cristianoag/trhmsx/images/2023-11-26_15-43.png

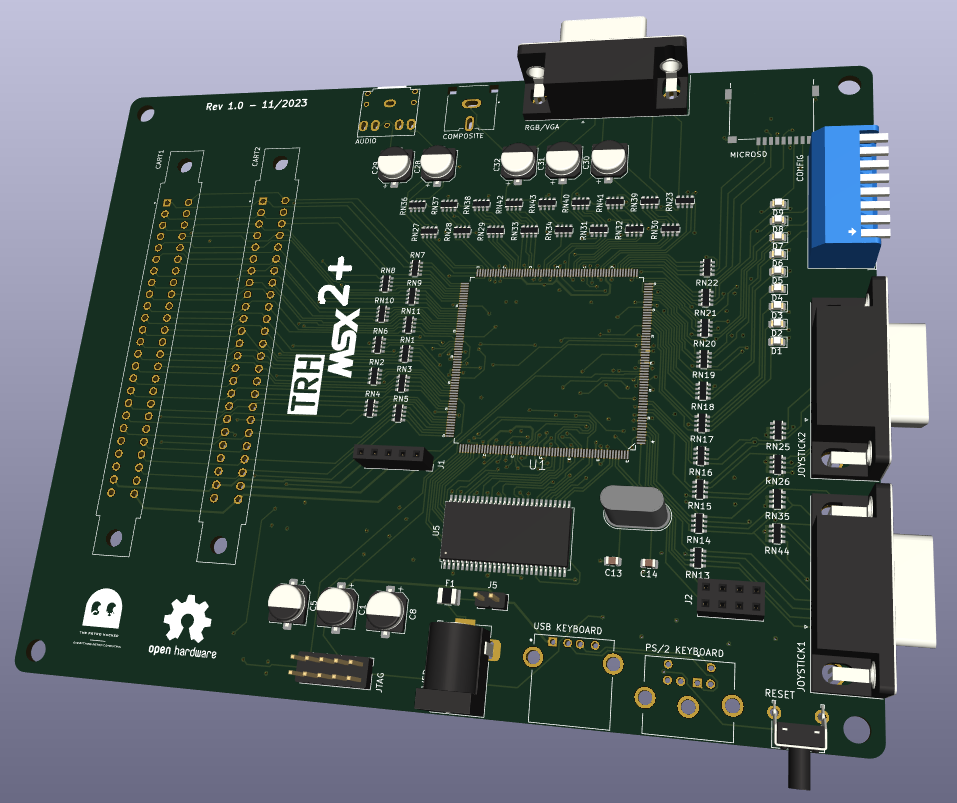
images/2023-11-26_15-43.png
