cristianoag/trhmsx/images/2024-02-25_20-27.png

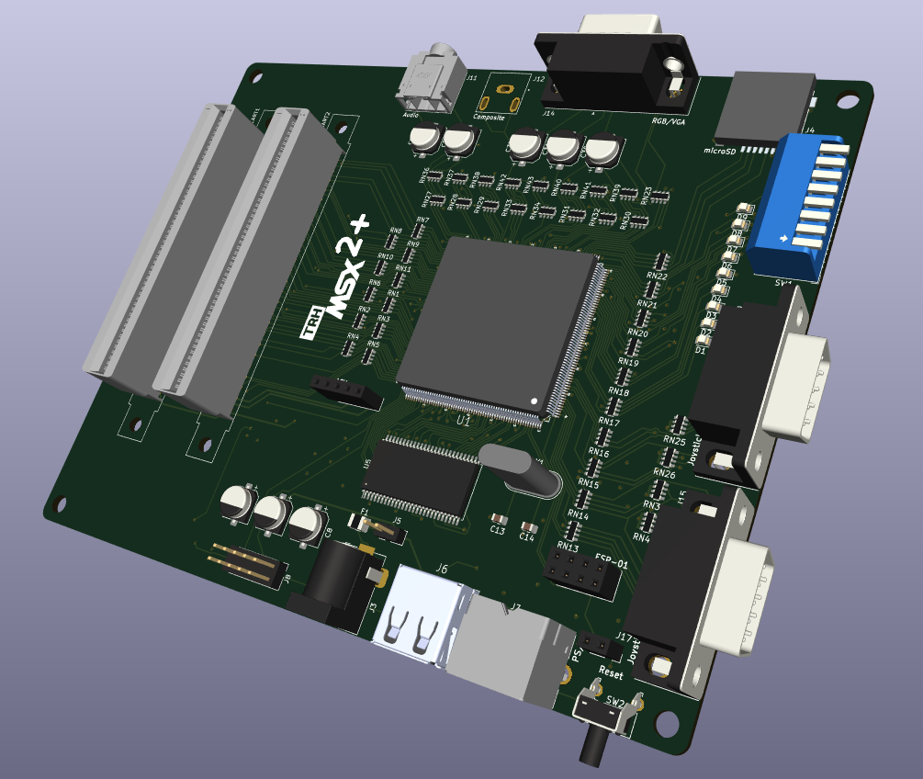
images/2024-02-25_20-27.png
