cristianoag/trhmsx/images/2024-02-25_21-25.png

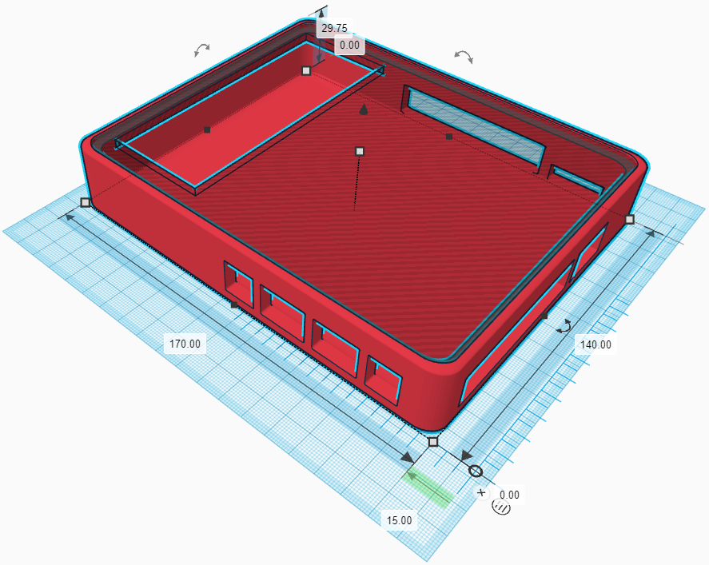
images/2024-02-25_21-25.png
