cristianoag/trhmsx/images/2024-04-27_21-23.png

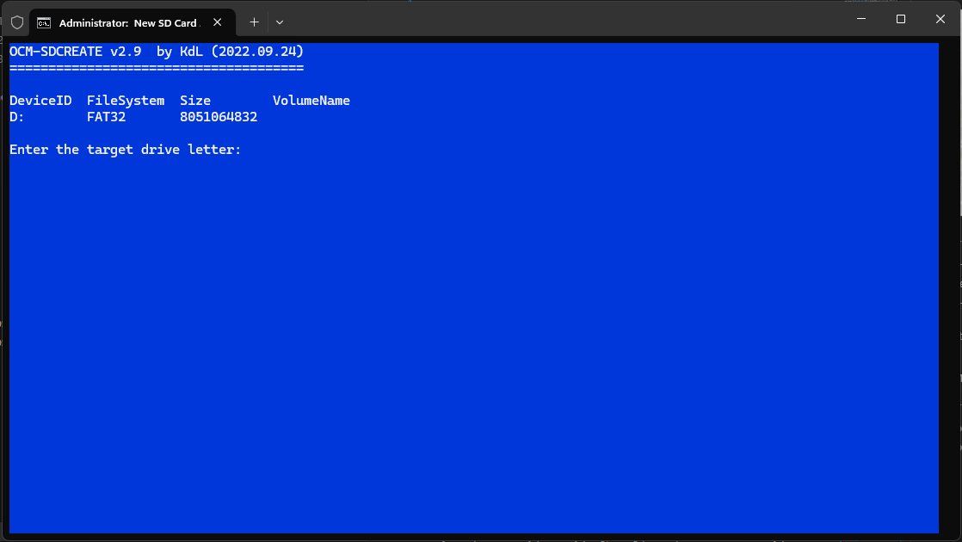
images/2024-04-27_21-23.png
