cristianoag/trhmsx/images/2024-04-27_21-33.png

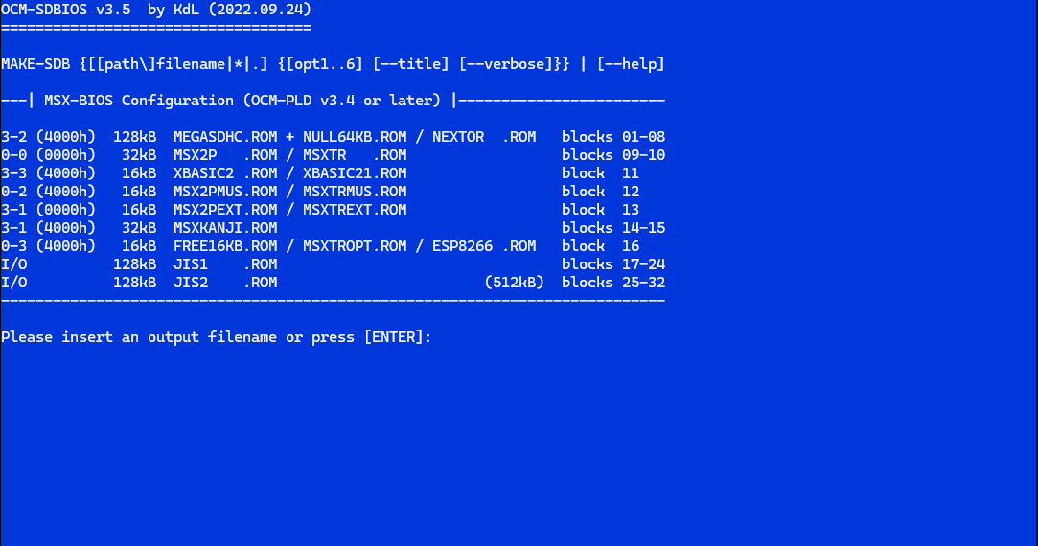
images/2024-04-27_21-33.png
